Sash-Reek2010/The-Meshp32/Assets/Case.png

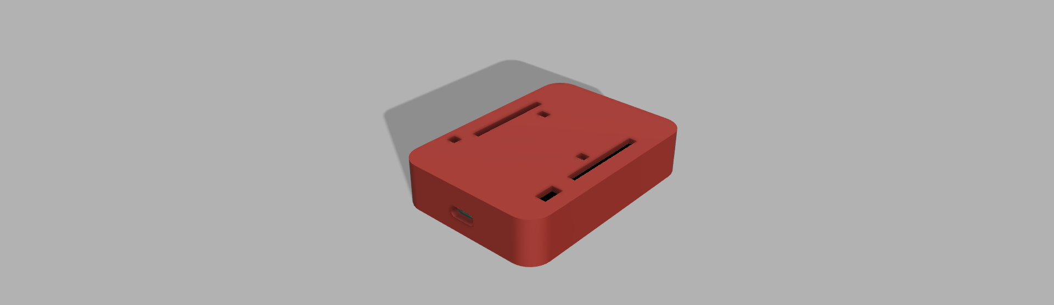
Assets/Case.png
